ma-ale/usbc_soldering_iron/3D/extenal-handle/RPC1-12RB-6P.step

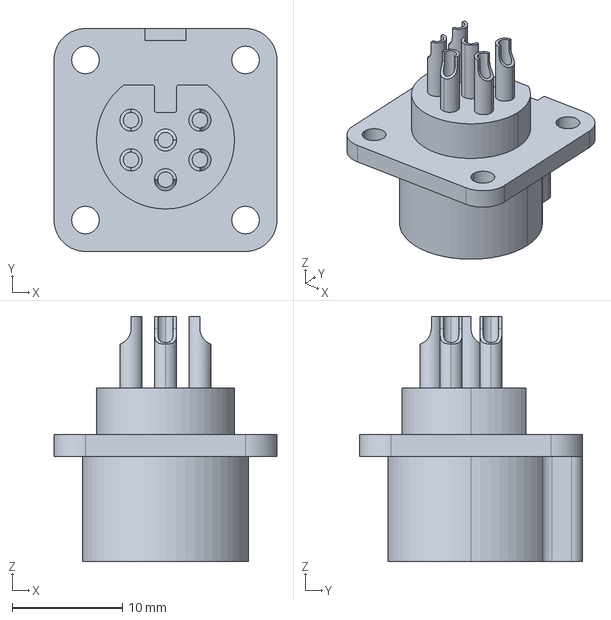
[picture p28: CAD file, 2026-03-21]
3D/extenal-handle/RPC1-12RB-6P.step
20.2 x 20.2 x 22.2 mm
