ma-ale/usbc_soldering_iron/3D/stylo/OLED_0.69_X069-9616TSWIG02-H14.FCStd

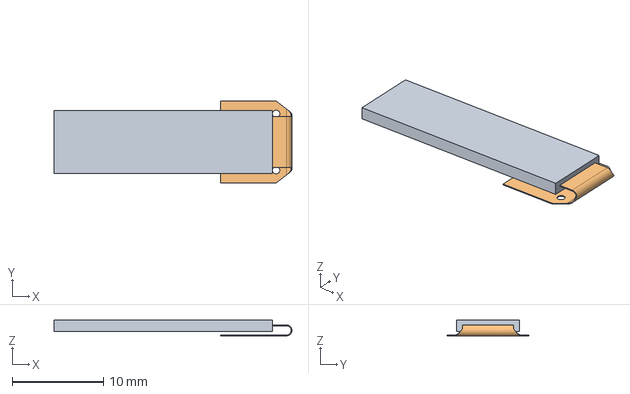
[picture p29: CAD file, 2026-06-11]
3D/stylo/OLED_0.69_X069-9616TSWIG02-H14.FCStd
26.1 x 9.00 x 1.73 mm
Screen
Cable
