ma-ale/usbc_soldering_iron/3D/extenal-handle/I2C_OLED.step

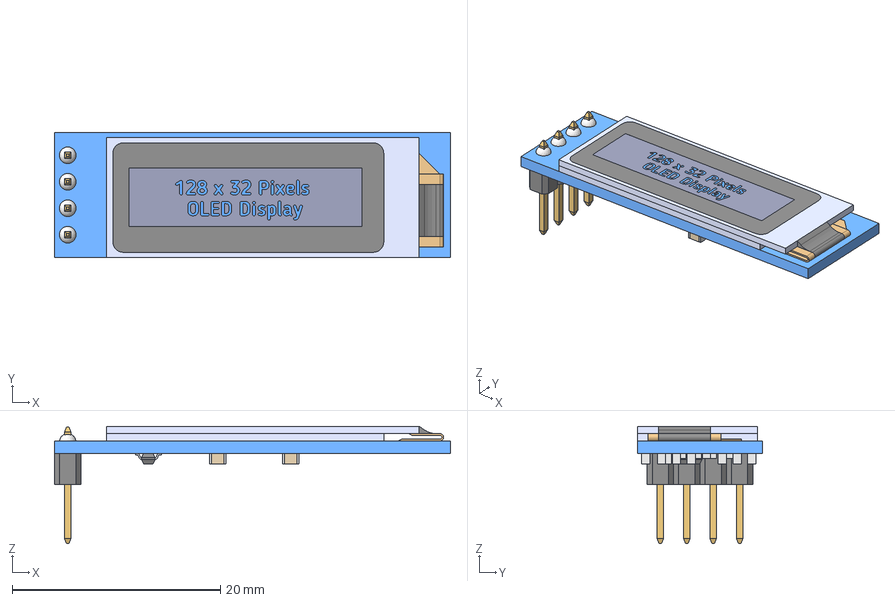
[picture p30: CAD file, 2026-03-21]
3D/extenal-handle/I2C_OLED.step
38.0 x 12.0 x 11.3 mm
Board_001
1x4 Male Header_001
0603 Capacitor_001
0603 Capacitor_002
0603 Capacitor_003
0603 Capacitor_004
0603 Capacitor_005
0603 Capacitor_006
0603 Capacitor_007
0603 Capacitor_008
0603 Resistor_001
0603 Resistor_002
0603 Resistor_003
0603 Resistor_004
0603 Resistor_005
Surface Mount Transistor_001
