ma-ale/usbc_soldering_iron/sim/MMASU32MAB7106_PNA01_LT.cir

* LTspice Encrypted File
* 
* This encrypted file has been supplied by a 3rd
* party vendor that does not wish to publicize
* the technology used to implement this library.
* 
* Permission is granted to use this file for
* simulations but not to reverse engineer its
* contents.
* 
* MMASU32MAB7106_PNA01     LTspice Model  ( Temperature / DC Bias Model )
*--------------------------------------------------------------------------------------------------------
* Model Generated by TAIYO YUDEN Corporation (https://www.yuden.co.jp/en/)
* Version 3.0
* TAIYO YUDEN Control No. 250905
* Copyright(c) 2021 TAIYO YUDEN CO.,LTD. All Rights Reserved.
*--------------------------------------------------------------------------------------------------------
* Product Description (link to TY-COMPAS)
* https://ds.yuden.co.jp/TYCOMPAS/or/detail?pn=MMASU32MAB7106KPNA01&u=M
*--------------------------------------------------------------------------------------------------------
* 
* Begin:
 1E FD 14 DB 52 AE 58 6A 2E 81 BB EB 90 C3 0B 2A
 41 F4 3F AB F8 54 DD 0D 1E 08 9B 9B 3B 9B 47 A7
 EC B5 42 B7 92 B1 22 50 FC 89 DD 35 F1 E7 B8 26
 F0 C3 6C 8D A8 FB AC FD EA B2 BF 0A 8E 42 06 33
 EE F3 B3 AE 40 5F 78 0B 48 12 2D 03 C2 66 80 EE
 D0 C4 83 02 D6 2D C0 CD 42 D7 66 53 C4 6B 17 0E
 30 FF 6B 2E 99 B6 D5 BF 3E F8 CD 11 4C 08 95 08
 75 00 04 36 B3 0D E7 0D D2 01 DA E3 F9 C5 AE A6
 35 9E 29 2A AA C6 D2 7B 1D E5 F1 28 60 3B 6F 46
 40 EF 64 B4 BF 18 72 32 E2 01 BF F0 7A C5 9C 57
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
 14 13 74 B8 14 4C AB 4B 69 51 90 BF 4B 80 D0 74
 F2 5C 52 5A 05 3A 16 61 23 66 63 E9 1F A4 0A FF
 86 A0 F0 C7 8B 78 2C 5B 27 7A 91 CF 75 3C 08 68
 53 02 D2 C8 A6 E0 5A 30 19 FA 58 6D 7B F1 EA C3
 1B 81 8F 39 0D 5F F4 BB 6C 08 C3 69 D8 E6 35 45
 31 3B 5C 29 45 8E D3 B5 68 B7 96 E1 0C 91 B5 C5
 00 FA 6E D7 D4 5F CE CC 37 EA 46 C6 A1 DA 37 2F
 44 9B 2A F2 63 95 B0 48 2F CE 6A D9 1E AA 5A 3E
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
