ma-ale/usbc_soldering_iron/sim/pi_filter.asc

C1: cap; 5p
C2: HHXC350ARA220ME61G
C3: cap; 100n
C4: cap; 10p
C5: cap; 1µ
C6: cap; 200µ
D1: diode; RB068M-60
D5: schottky; 1N5818
L1: ind; flux={L*Is}*tanh(x/{Is})
L2: ind; 500n; Rser=1m
L3: ind; 10n; Rser=1m
M1: nmos; AON7140
R1: res; {rtip}
R2: res; 5m
R3: res; 12m
R4: res; 10Meg
R8: res; 120m
R9: res; 20m
S1: sw; SW1
U1: MMASU32MAB7106_PNA01; Temperature=40
U2: IRS10752L
U3: MMASU32MAB7106_PNA01; Temperature=40
U4: MMASU32MAB7106_PNA01; Temperature=40
U5: MMASU32MAB7106_PNA01; Temperature=40
U6: MMASU32MAB7106_PNA01; Temperature=40
V1: voltage; {vbus}
V2: voltage; 12
V3: voltage; PULSE(0 5 5m 100n 100n {d*1/fsw} {1/fsw} 200)
V4: voltage; PWL(0 0 1m 0 1.1m 1 6m 1 6.1m 0)
Named nets: 0, vbus, vmid, vdrv, cp
.tran 12m
.param fsw=100k
.param d={pout/(vbus*vbus/rtip)}
.param vbus=28
.param pout=130
.param rtip=2.5
.lib IRS10752L.lib
.param vcc=3.3
.options abstol=10n vntol=10n reltol=0.005 gmin=10p method=gear
.param L=2.2u Is=7
*.step param rtip list 2.5 3 3.5  4.5 5 100k
.model SW1 SW(Ron=1n  Roff=10Meg Vt=0.5 Vh=0.1)
