ma-ale/usbc_soldering_iron/sim/MCASU32MAB7106_PNA01_LT.cir

* LTspice Encrypted File
* 
* This encrypted file has been supplied by a 3rd
* party vendor that does not wish to publicize
* the technology used to implement this library.
* 
* Permission is granted to use this file for
* simulations but not to reverse engineer its
* contents.
* 
* MCASU32MAB7106_PNA01     LTspice Model  ( Temperature / DC Bias Model )
*--------------------------------------------------------------------------------------------------------
* Model Generated by TAIYO YUDEN Corporation (https://www.yuden.co.jp/en/)
* Version 3.0
* TAIYO YUDEN Control No. 250905
* Copyright(c) 2021 TAIYO YUDEN CO.,LTD. All Rights Reserved.
*--------------------------------------------------------------------------------------------------------
* Product Description (link to TY-COMPAS)
* https://ds.yuden.co.jp/TYCOMPAS/or/detail?pn=MCASU32MAB7106KPNA01&u=M
*--------------------------------------------------------------------------------------------------------
* 
* Begin:
 A2 FC 2B C7 10 2D 69 7F 68 E6 80 19 46 5C D9 F6
 0D 45 BF C5 A0 5A 3A F2 D9 51 EC C3 35 EC 0C 64
 48 C1 75 AA F6 EB 1A AD 2E A1 36 AD 64 24 A4 F9
 C0 0A 91 66 85 E4 BE 43 A0 25 9C 72 63 EB C1 31
 8F B8 57 D8 9C 6E 97 3B C8 51 26 0B 14 2E BE 49
 10 A6 BA 70 C3 36 1D A9 F3 D5 4B C0 DB 9A 03 E0
 D8 57 75 0B 1C E1 29 1B 3C E7 11 C8 AC C1 A6 CA
 45 0D D4 96 8C 69 27 CC 58 34 E7 DD CA 0F 04 0C
 66 85 29 9B D5 23 A6 8A 0E CE 7B C9 74 8D 2B EC
 C7 12 9A CE 9E E3 34 03 11 34 3B 75 D6 37 5C 9F
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
 5C 62 DF 05 BD 2C 29 49 7E 1C 95 9B 64 14 97 43
 0F 4B 62 72 49 9C 90 58 41 B8 C2 10 7A 7F BF BA
 FF 88 F9 52 87 5E 3C 37 8F D1 61 EA E0 B9 7F 9C
 D5 83 60 7D BE 2B CE 1D D0 2C 10 6B 92 DD E1 98
 6A 1A B3 F9 0E C1 5F E1 3B F3 20 D3 8C 9D EB 00
 55 2B 53 DB C2 4D 59 41 F8 38 8F 75 6D 02 05 14
 70 E5 77 90 A7 5B 1B D1 30 E7 50 BF 57 82 3E 12
 40 38 9F 6C 93 03 1A 4D 7F 97 58 44 C1 83 EF B7
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
