ma-ale/usbc_soldering_iron/sim/simple_buck.asc

C1: cap; 88µ
C2: cap; 44µ
D1: schottky; RB078BGE30S
D2: zener; BZX84C12VLY
L1: ind; 2.2µ; Rser=22m
M1: pmos; AONR21307
Q1: npn; 2N2222
R1: res; 5m
R2: res; 2.5
R3: res; 1k
R4: res; 0
R5: res; 10k
V1: voltage; 20; Rser=0.05
V2: voltage; PULSE(0 3.3 1m 1n 1n {ton} {period} 1k); halfsine
Named nets: 0, PWM, out
.tran 0 2m 1m
.param freq=100k
.param duty=0.2
.param period=1/{freq} ton={duty}*{period}
