ma-ale/usbc_soldering_iron/sim/chopper.asc

C1: cap; 100µ; Rser=5m
D1: diode; MBR745
L1: ind; 1.5µ; Ipk=10 Rser=20m Cpar=10p
M1: pmos; Si4427DY
M2: pmos; Si4427DY
Q1: npn; 2N2222
Q2: pnp; 2N2907
Q3: npn; 2N2222
Q4: pnp; 2N2907
R1: res; 2.5
V1: voltage; 28; Rser=1m
V2: voltage; PULSE(0 10 0 10n 10n {ton} {t} 1k)
V3: voltage; PULSE(0 10 {twait} 100n 100n {toff} {t} 1k)
Named nets: 0, out, in, mid
.tran 3m uic
.ic V(C1)=0 I(L1)=0
.param freq=50k d=0.42
.param ton={d}/{freq}
.param t=1/{freq}
.param toff=(((1-{d})/{freq})*0.9)
.param twait={toff}-((1-{d})*t - {toff})
