ma-ale/usbc_soldering_iron/sim/two_phase_buck.asc

C1: cap; {C}; Rser=5m
C2: cap; 100n
C3: cap; {C}; Rser=5m
C4: cap; 100n
C5: cap; 10000µ
D1: diode; 1N5819
D2: diode; 1N5819
L1: ind; {L}; Rser=10m
L2: ind; {L}; Rser=10m
M1: nmos; AONP36336_Q1
M2: nmos; AONP36336_Q2
M3: nmos; AONP36336_Q1
M4: nmos; AONP36336_Q2
R1: res; 100
U1: LTC4442
U3: LTC4442
V1: voltage; 28; Rser=1m
V2: voltage; 5
V3: voltage; PULSE(0 5 0 10n 10n {ton} {tsw} 1k)
V4: voltage; PULSE(0 5 {td} 10n 10n {ton} {tsw} 1k)
Named nets: 0, vcc, vbus, pwm1, pwm2, out
.param fsw=1000k
.param L=1u C=22u
.param tsw=1/{fsw}
.param d=0.32
.param ton={tsw}*{d}
.tran 1m
.param trf=10n
.param td={tsw}/2
